simoninns/Beeb-Bot/stl/cover.stl

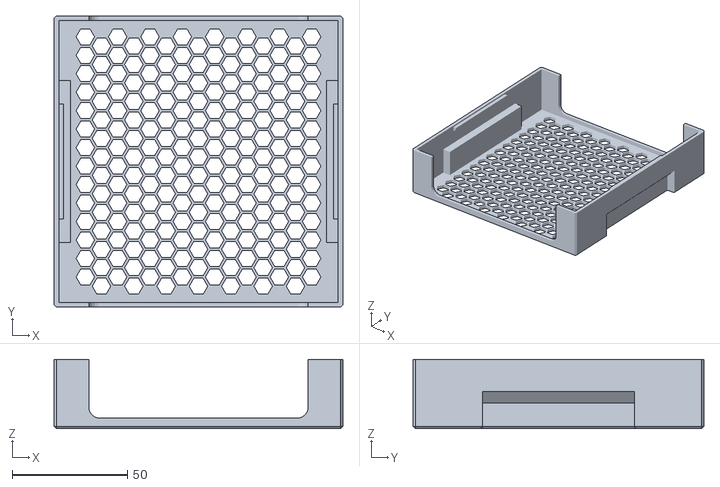
[picture p15: CAD file, 2020-05-15]
stl/cover.stl
125.0 x 126.0 x 30.0
