simoninns/Beeb-Bot/stl/ball_caster_holder.stl

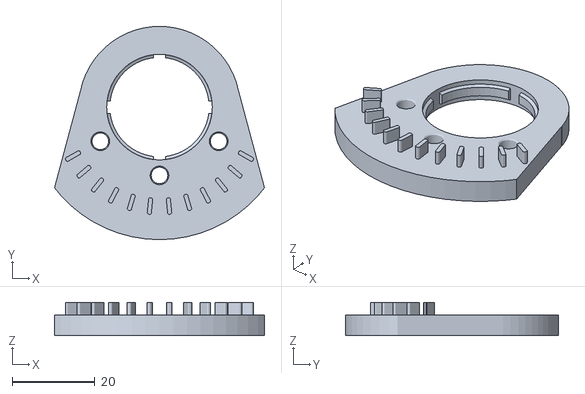
[picture p16: CAD file, 2020-05-15]
stl/ball_caster_holder.stl
50.7 x 51.5 x 8.00
