simoninns/Beeb-Bot/stl/alu_profile_120mm.stl

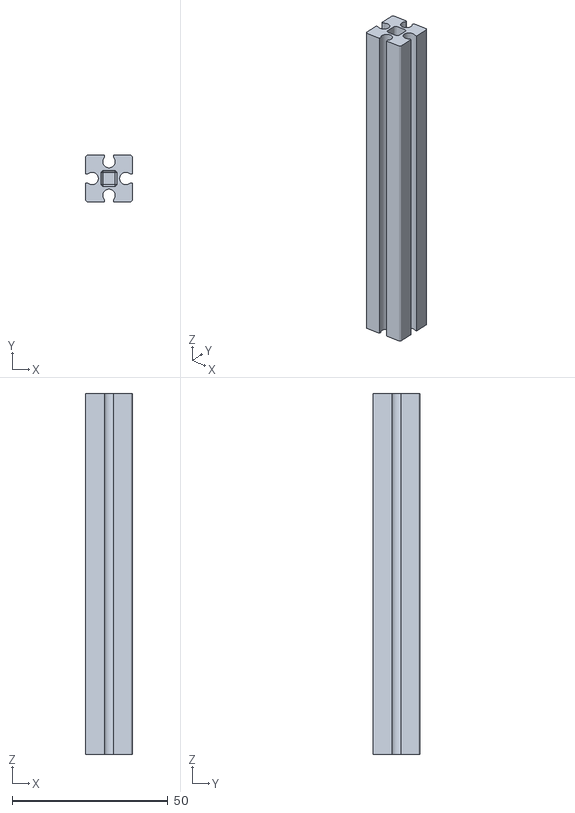
[picture p17: CAD file, 2020-05-15]
stl/alu_profile_120mm.stl
15.0 x 15.0 x 116.0
