simoninns/Beeb-Bot/stl/chain_20links.stl

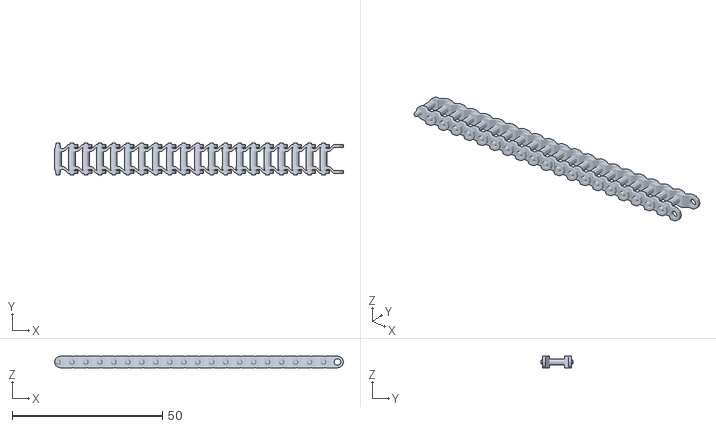
[picture p18: CAD file, 2020-05-15]
stl/chain_20links.stl
96.2 x 10.5 x 4.00
