simoninns/Beeb-Bot/stl/large_pulley_wheel.stl

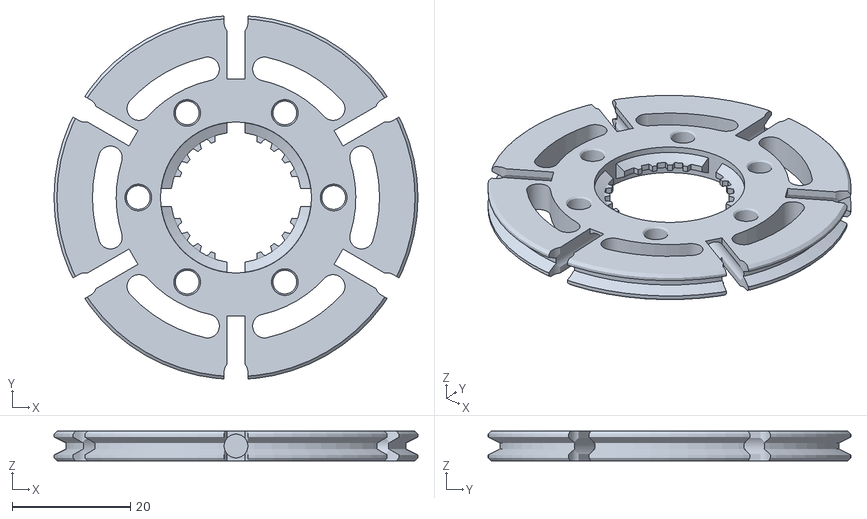
[picture p19: CAD file, 2020-05-15]
stl/large_pulley_wheel.stl
61.5 x 61.3 x 5.00
