simoninns/Beeb-Bot/stl/block_7p5mm.stl

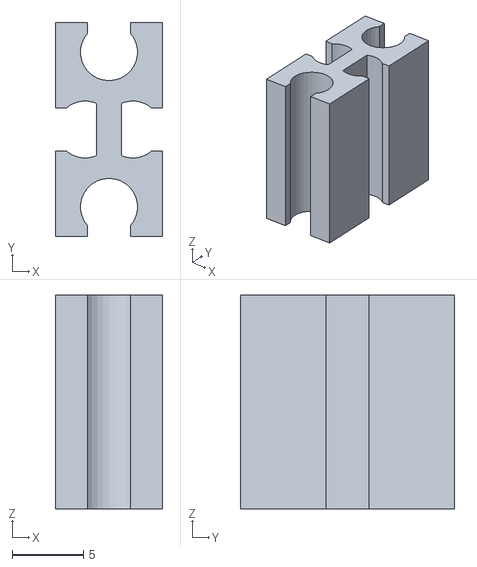
[picture p20: CAD file, 2020-05-15]
stl/block_7p5mm.stl
7.50 x 15.0 x 15.0
