simoninns/Beeb-Bot/stl/mini_switch_base.stl

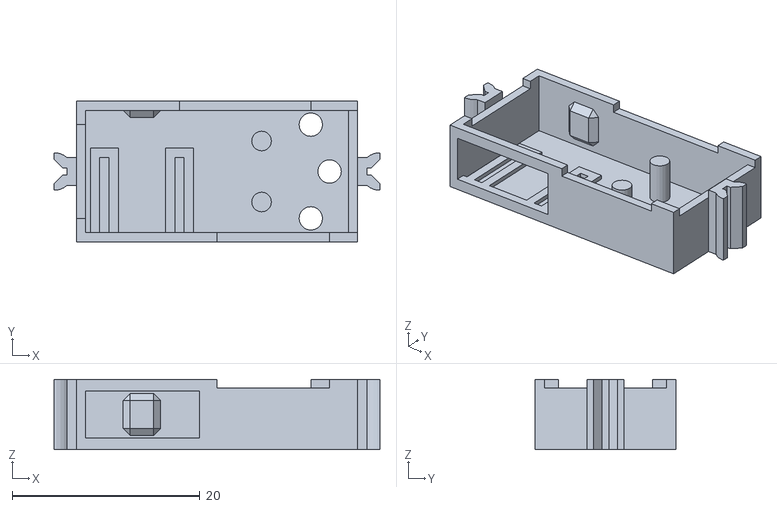
[picture p21: CAD file, 2020-05-15]
stl/mini_switch_base.stl
34.8 x 15.0 x 7.50
