simoninns/Beeb-Bot/stl/alu_profile_endcap_x1.stl

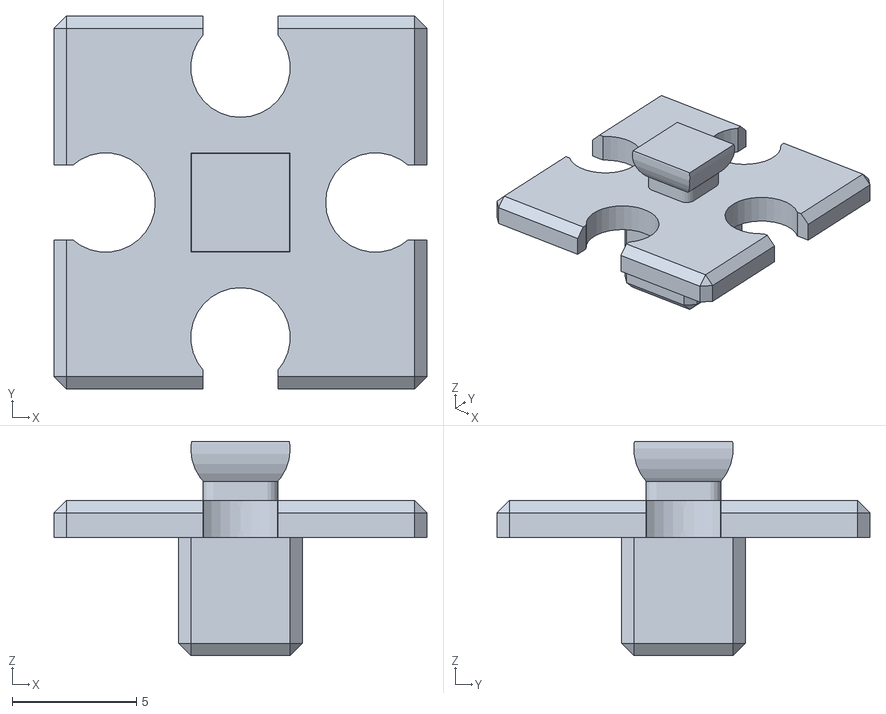
[picture p22: CAD file, 2020-05-15]
stl/alu_profile_endcap_x1.stl
15.0 x 15.0 x 8.62
