simoninns/Beeb-Bot/stl/grey_axle_x13.stl

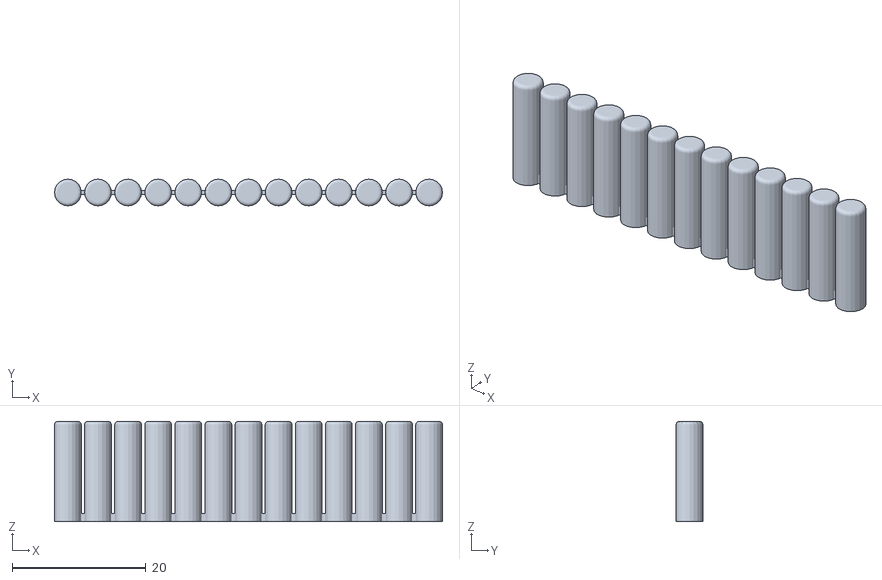
[picture p23: CAD file, 2020-05-15]
stl/grey_axle_x13.stl
58.0 x 4.00 x 15.0
