simoninns/Beeb-Bot/stl/block_v15.stl

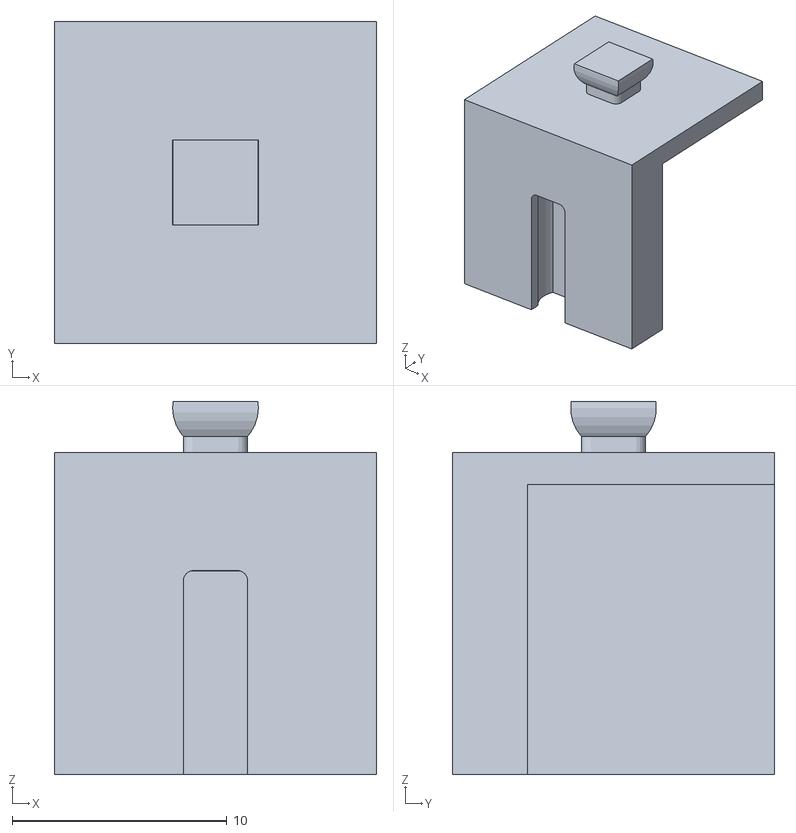
[picture p24: CAD file, 2020-05-15]
stl/block_v15.stl
15.0 x 15.0 x 17.4
