simoninns/Beeb-Bot/stl/block_5mm.stl

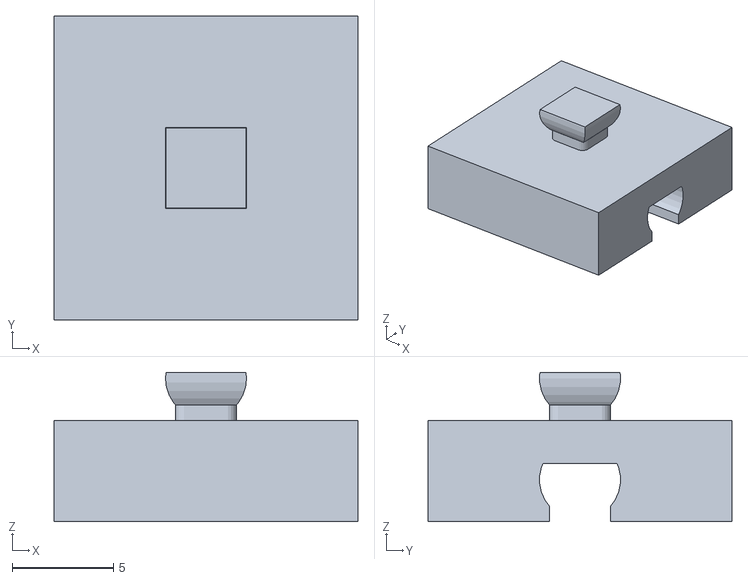
[picture p25: CAD file, 2020-05-15]
stl/block_5mm.stl
15.0 x 15.0 x 7.38
