simoninns/Beeb-Bot/stl/alu_profile_endcap_x28.stl

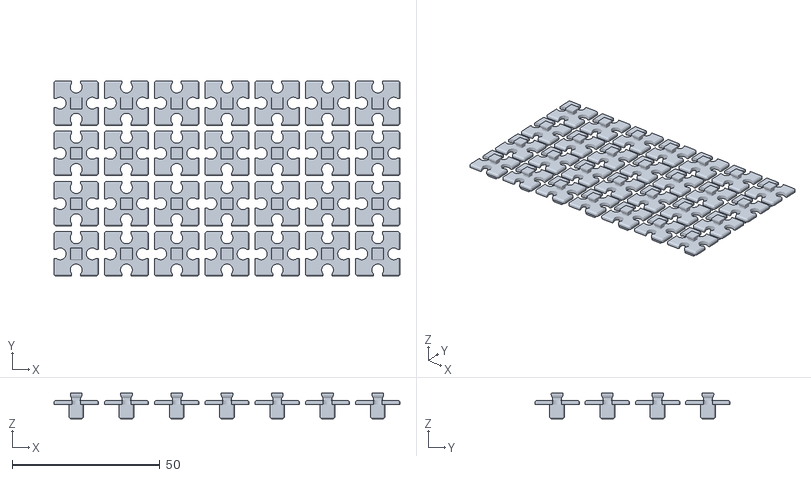
[picture p26: CAD file, 2020-05-15]
stl/alu_profile_endcap_x28.stl
117.0 x 66.0 x 8.62
