simoninns/Beeb-Bot/stl/hub_top.stl

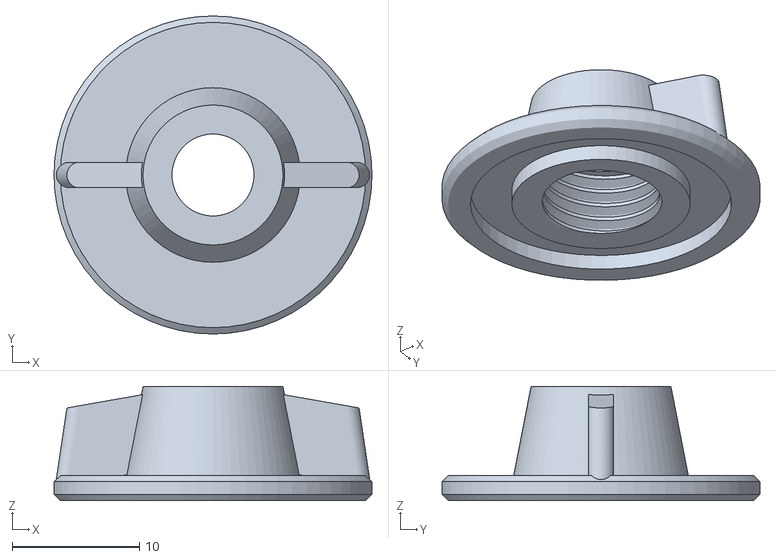
[picture p27: CAD file, 2020-05-15]
stl/hub_top.stl
25.0 x 25.0 x 9.00
