simoninns/Beeb-Bot/stl/philips_cog_wheel_bottom.stl

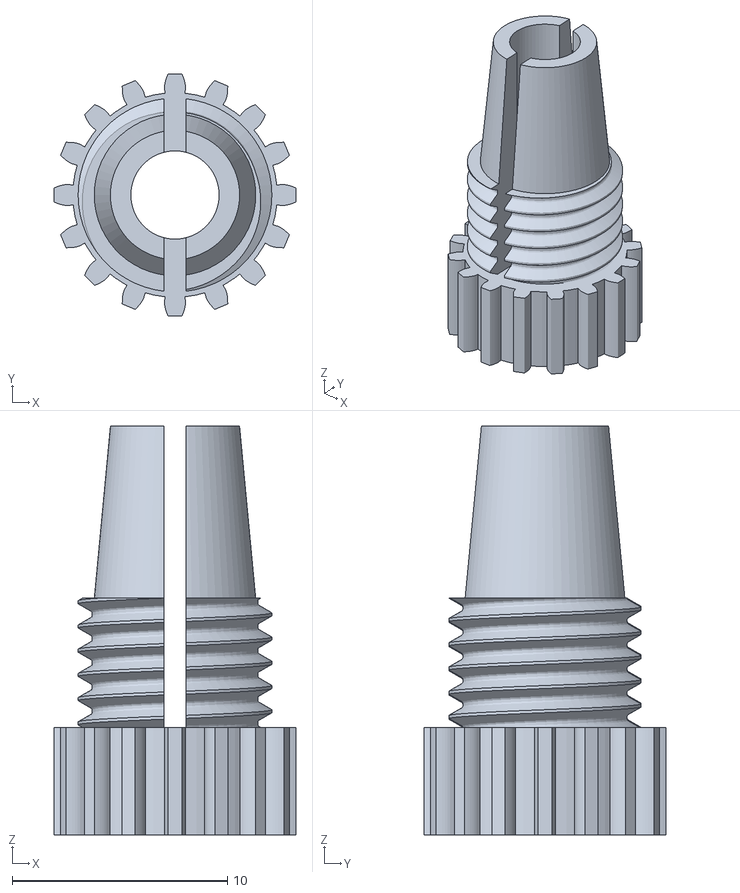
[picture p28: CAD file, 2020-05-15]
stl/philips_cog_wheel_bottom.stl
11.2 x 11.2 x 19.0
