simoninns/Beeb-Bot/stl/alu_profile_90mm.stl

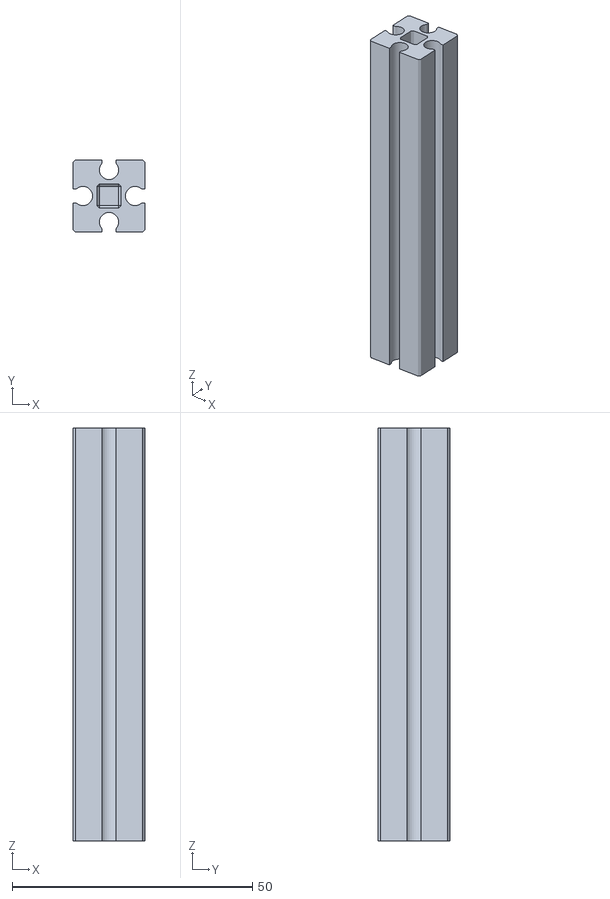
[picture p29: CAD file, 2020-05-15]
stl/alu_profile_90mm.stl
15.0 x 15.0 x 86.0
