simoninns/Beeb-Bot/stl/block_15mm.stl

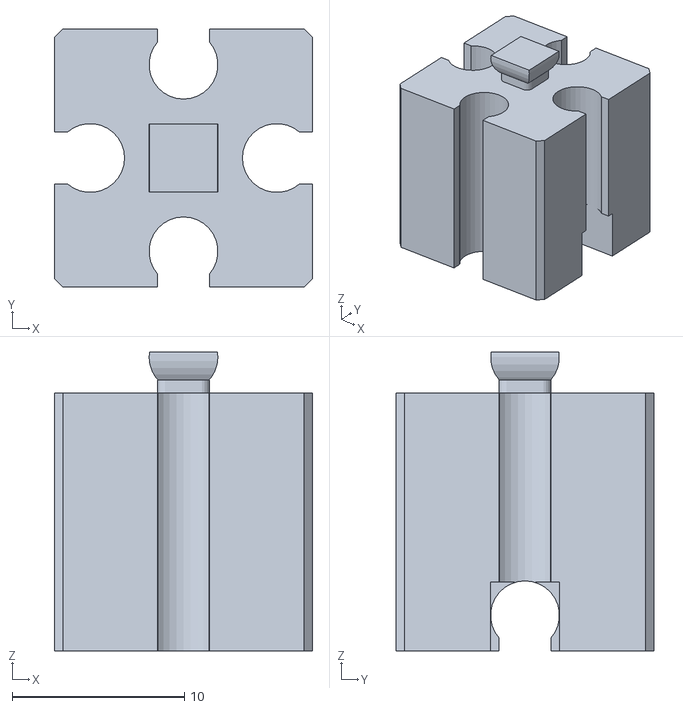
[picture p30: CAD file, 2020-05-15]
stl/block_15mm.stl
15.0 x 15.0 x 17.4
