simoninns/Beeb-Bot/stl/nema17_mount.stl

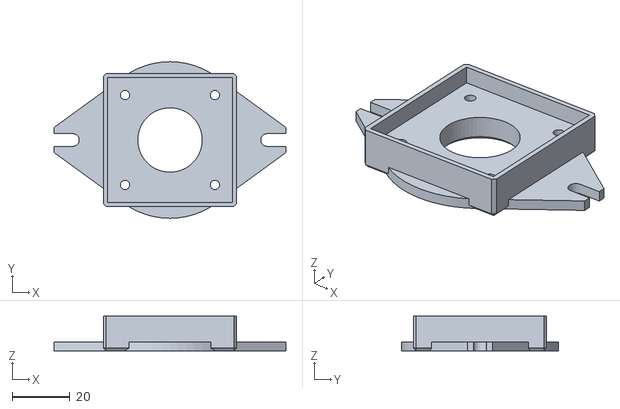
[picture p31: CAD file, 2020-05-15]
stl/nema17_mount.stl
80.0 x 54.0 x 12.0
