simoninns/Beeb-Bot/stl/nema17_cog_wheel_bottom.stl

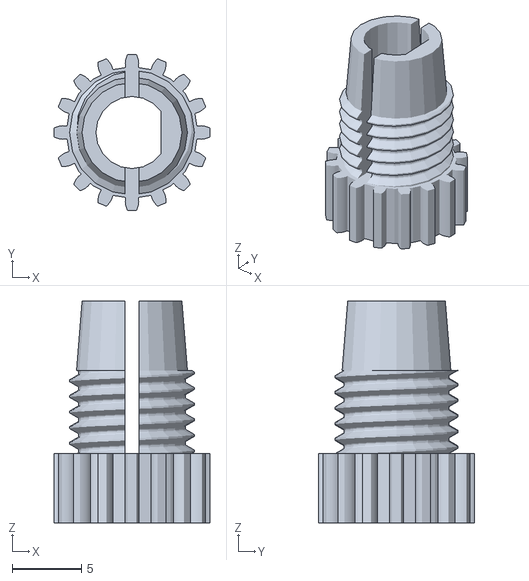
[picture p32: CAD file, 2020-05-15]
stl/nema17_cog_wheel_bottom.stl
11.2 x 11.2 x 16.0
