simoninns/Beeb-Bot/stl/v_axle_x6.stl

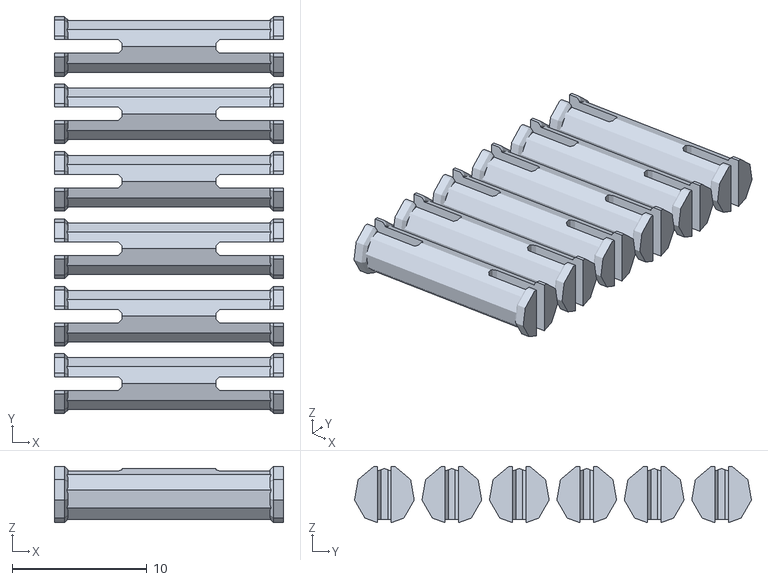
[picture p33: CAD file, 2020-05-15]
stl/v_axle_x6.stl
17.0 x 29.4 x 4.18
