simoninns/Beeb-Bot/stl/hinge_block.stl

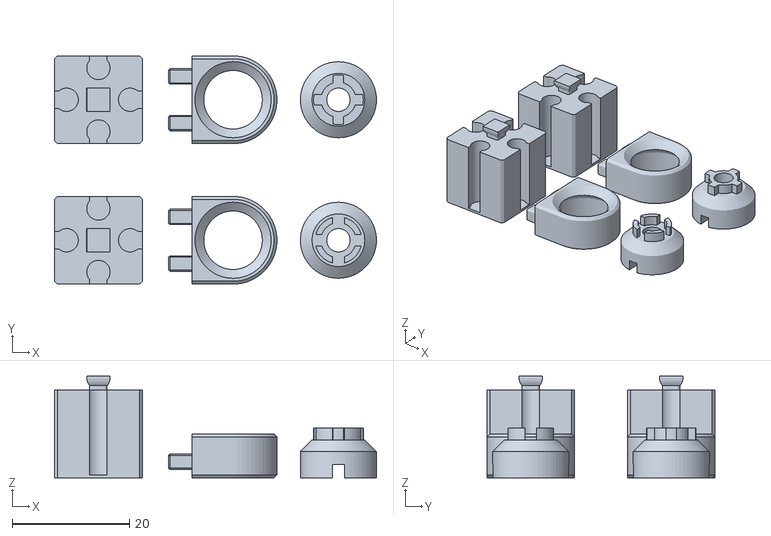
[picture p34: CAD file, 2020-05-15]
stl/hinge_block.stl
55.0 x 39.0 x 17.4
