simoninns/Beeb-Bot/stl/plate_sr_15x90mm.stl

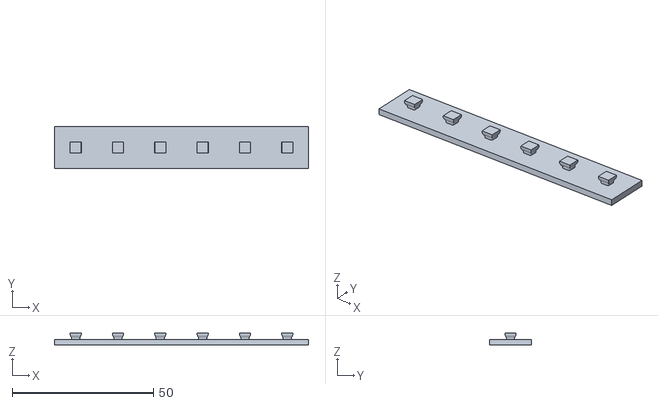
[picture p35: CAD file, 2020-05-15]
stl/plate_sr_15x90mm.stl
90.0 x 15.0 x 4.38
